AlbertoAncilotto/Arduino_TPA3116_Amp/images/IMG_20201020_144350.jpg

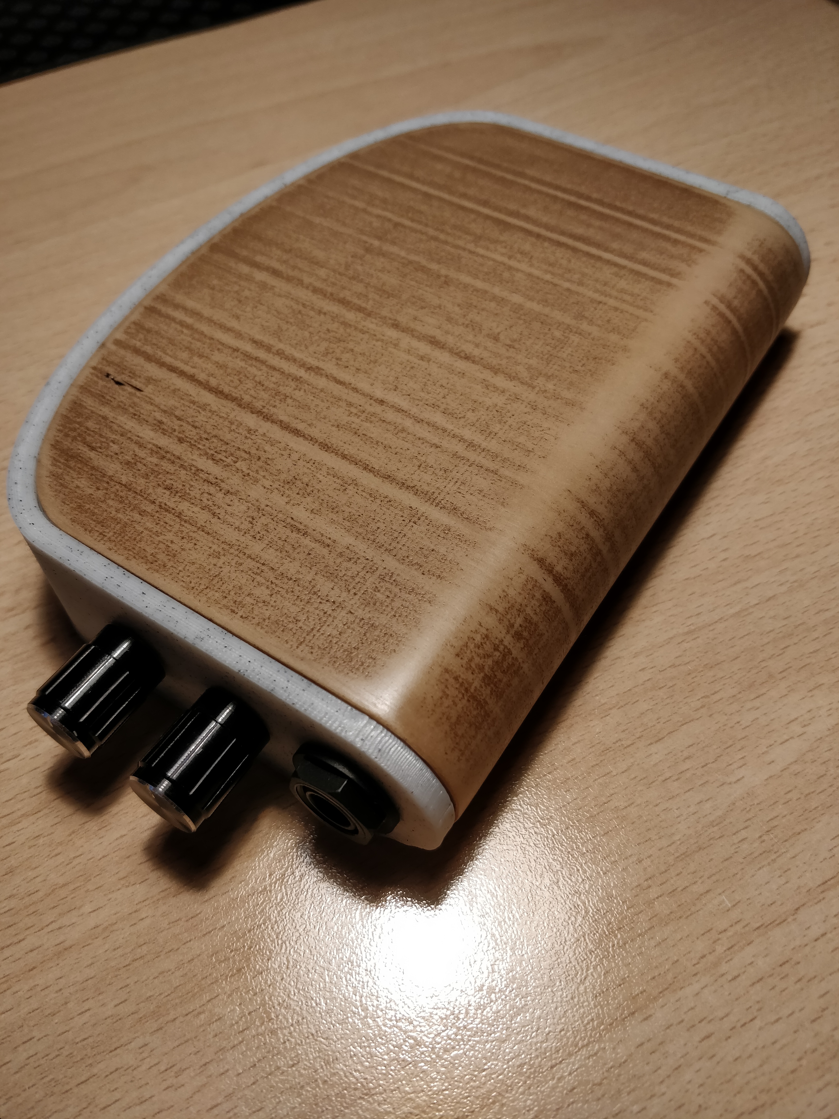
images/IMG_20201020_144350.jpg
