AlbertoAncilotto/Arduino_TPA3116_Amp/images/IMG_20201020_153747.jpg

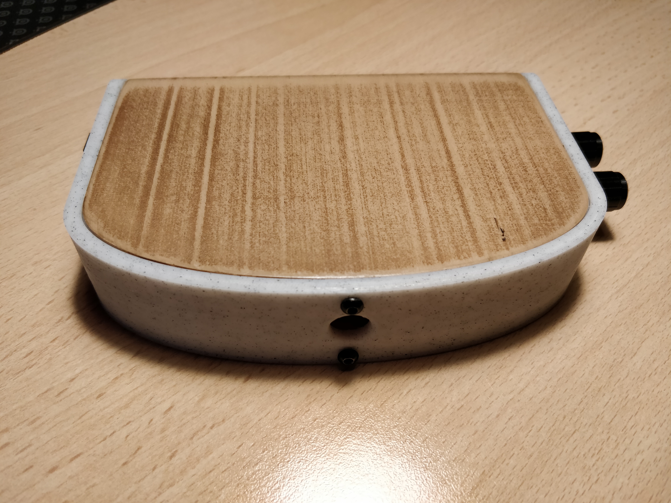
images/IMG_20201020_153747.jpg
